alencibi27-arch/electronic-thermometer-kicad/AL-P060I.kicad_sch

## KiCad design AL-P060I.kicad_sch (2026-08-26)

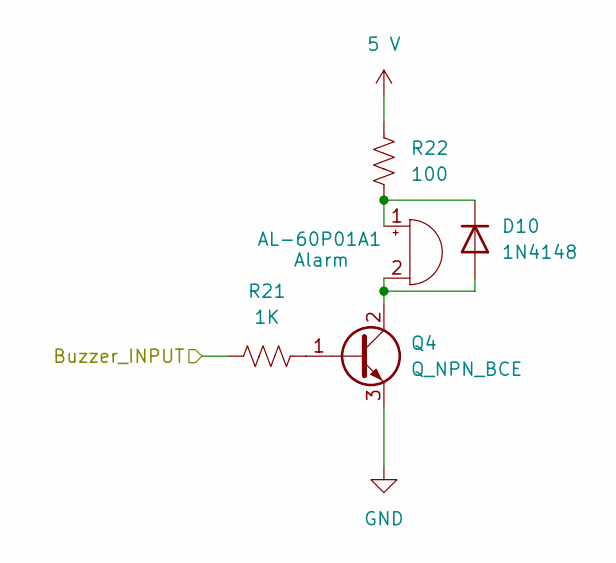
[picture p8: schematic AL-P060I.kicad_sch]

Parts:
AL-60P01A1: Alarm; AL-60P01A___; Rated Voltage 1.5V; Operating Voltage 1.5V
D10: 1N4148; D_SOD-123
Q4: Q_NPN_BCE; TO-92_Inline
R21: 1K; R_0805_2012Metric
R22: 100; R_0805_2012Metric

Connections:
Buzzer_INPUT: R21.1
GND: Q4.3 (E)
unnamed: AL-60P01A1.1 (+), D10.1 (K), R22.2
unnamed: AL-60P01A1.2 (-), D10.2 (A), Q4.2 (C)
unnamed: Q4.1 (B), R21.2
V: R22.1
