alencibi27-arch/electronic-thermometer-kicad/ALARM_SUBSYSTEM.kicad_sch

## KiCad design ALARM_SUBSYSTEM.kicad_sch (2026-08-26)

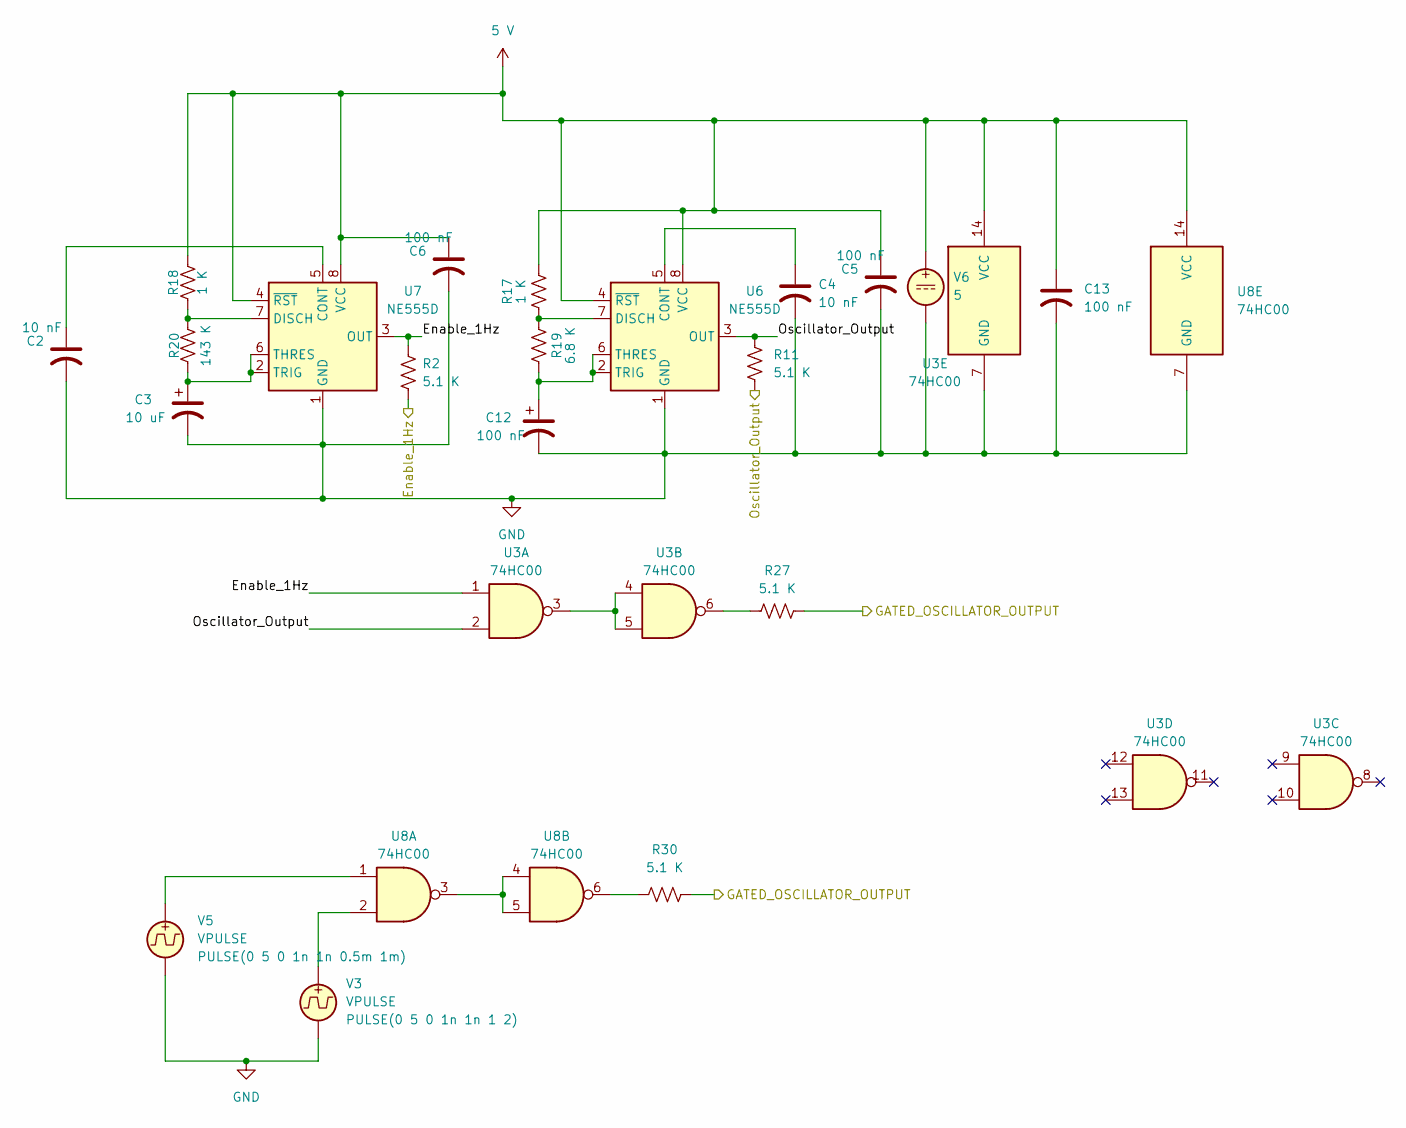
[picture p9: schematic ALARM_SUBSYSTEM.kicad_sch]

Parts:
C2, C4: 10 nF; C_1206_3216Metric
C3: 10 uF; CP_Radial_D5.0mm_P2.00mm
C5, C6, C13: 100 nF; C_1206_3216Metric
C12: 100 nF; CP_Radial_D5.0mm_P2.00mm
R2, R11, R27: 5.1 K; R_0805_2012Metric
R17, R18: 1 K; R_0805_2012Metric
R19: 6.8 K; R_0805_2012Metric
R20: 143 K; R_0805_2012Metric
R30: 5.1 K
U3: 74HC00; SOIC-14_3.9x8.7mm_P1.27mm
U6, U7: NE555D; SOIC-8_3.9x4.9mm_P1.27mm
U8: 74HC00
V3, V5: VPULSE
V6: 5

Connections:
Enable_1Hz: R2.1, R2.2, U3.1, U7.3 (OUT)
GATED_OSCILLATOR_OUTPUT: R27.1, R30.1
GND: C2.2, C3.2, C4.2, C5.2, C6.2, C12.2, C13.2, U3.7 (GND), U6.1 (GND), U7.1 (GND), U8.7 (GND), V3.2, V5.2, V6.2
unnamed: C2.1, U7.5 (CONT)
unnamed: C3.1, R20.1, U7.2 (TRIG), U7.6 (THRES)
unnamed: C4.1, U6.5 (CONT)
unnamed: C12.1, R19.2, U6.2 (TRIG), U6.6 (THRES)
unnamed: R17.1, R19.1, U6.7 (DISCH)
unnamed: R18.1, R20.2, U7.7 (DISCH)
unnamed: R27.2, U3.6
unnamed: R30.2, U8.6
unnamed: U3.3, U3.4, U3.5
unnamed: U8.1, V5.1
unnamed: U8.2, V3.1
unnamed: U8.3, U8.4, U8.5
Oscillator_Output: R11.1, R11.2, U3.2, U6.3 (OUT)
V: C5.1, C6.1, C13.1, R17.2, R18.2, U3.14 (VCC), U6.4 (~RST), U6.8 (VCC), U7.4 (~RST), U7.8 (VCC), U8.14 (VCC), V6.1
