alencibi27-arch/electronic-thermometer-kicad/LED_STEP_DECODER.kicad_sch

## KiCad design LED_STEP_DECODER.kicad_sch (2026-08-26)

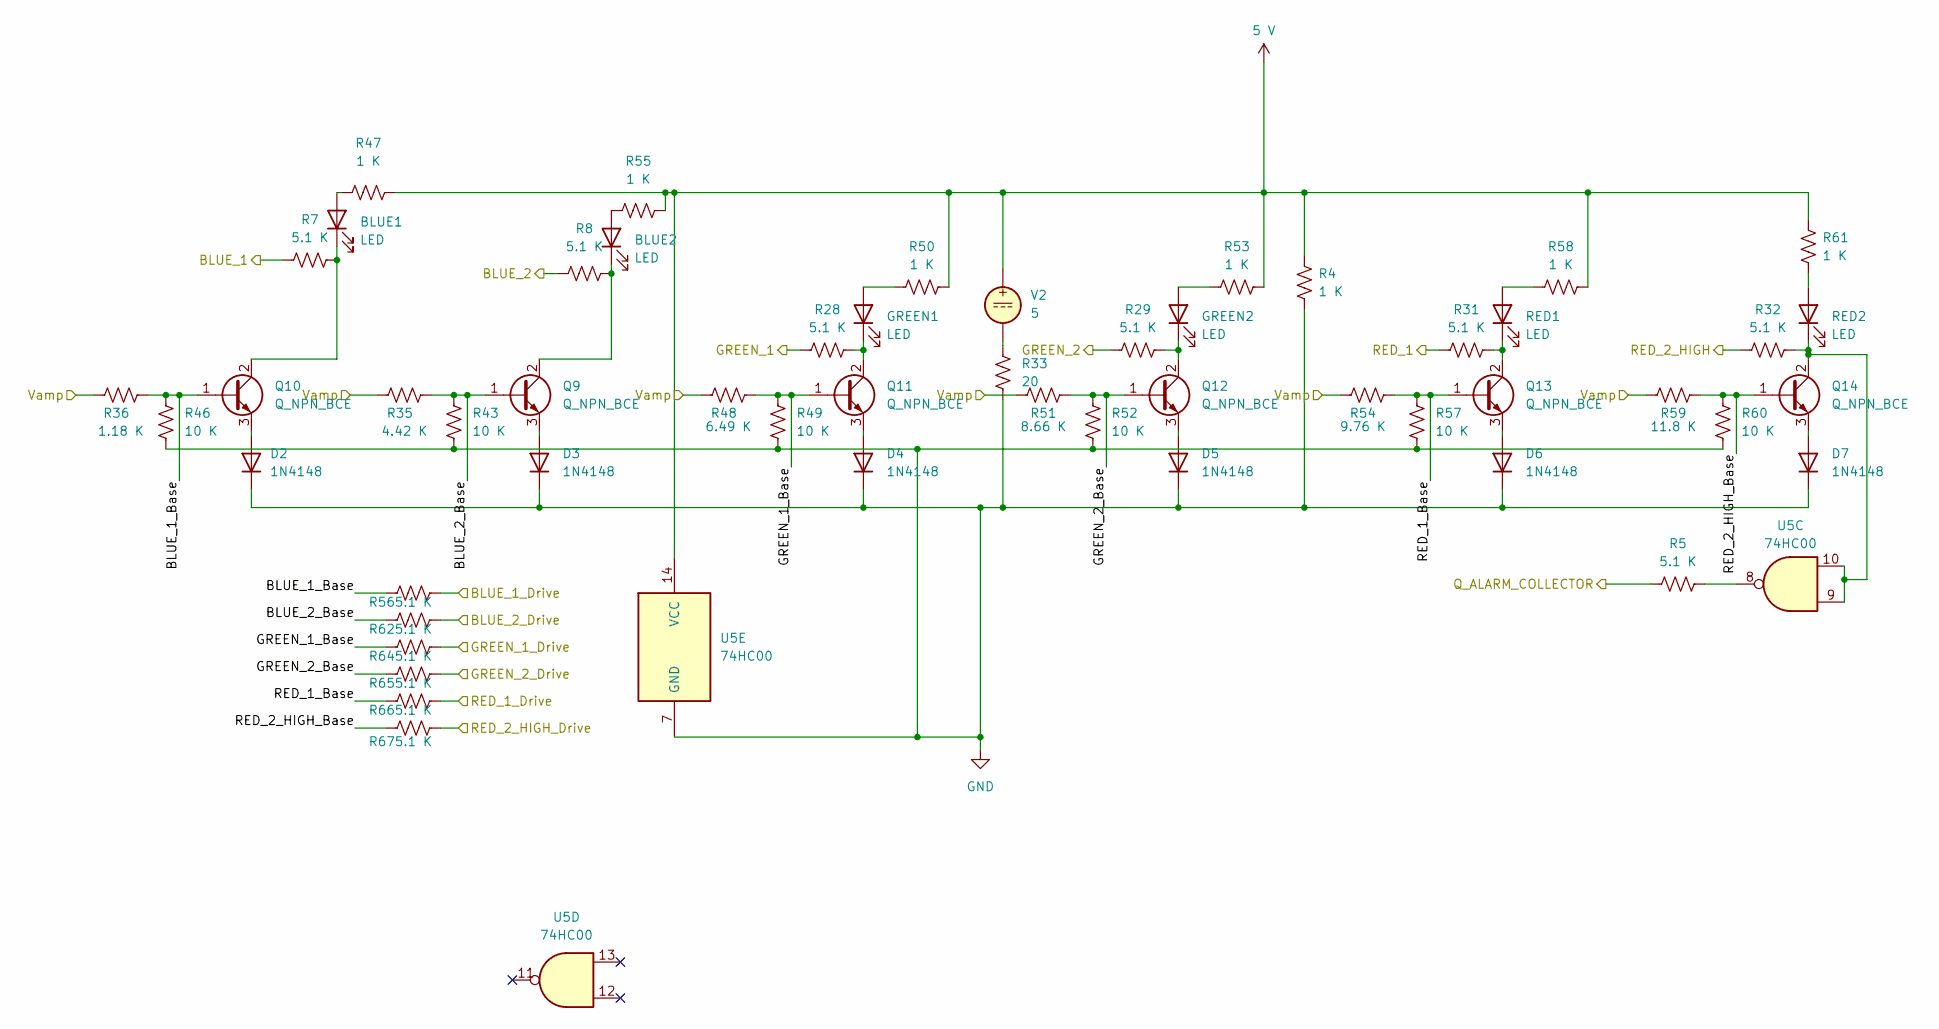
[picture p10: schematic LED_STEP_DECODER.kicad_sch]

Parts:
BLUE1, BLUE2: LED; LED_0805_2012Metric
D2, D3, D4, D5, D6, D7: 1N4148; D_DO-35_SOD27_P7.62mm_Horizontal
GREEN1, GREEN2: LED; LED_0805_2012Metric
Q9, Q10, Q11, Q12, Q13, Q14: Q_NPN_BCE; TO-92_Inline
R4, R47, R50, R53, R55, R58, R61: 1 K; R_0805_2012Metric
R5, R7, R8, R28, R29, R31, R32, R56, R62, R64, R65, R66, R67: 5.1 K; R_0805_2012Metric
R33: 20; R_0805_2012Metric
R35: 4.42 K; R_0805_2012Metric
R36: 1.18 K; R_0805_2012Metric
R43, R46, R49, R52, R57, R60: 10 K; R_0805_2012Metric
R48: 6.49 K; R_0805_2012Metric
R51: 8.66 K; R_0805_2012Metric
R54: 9.76 K; R_0805_2012Metric
R59: 11.8 K; R_0805_2012Metric
RED1, RED2: LED; LED_0805_2012Metric
U5: 74HC00; SOIC-14_3.9x8.7mm_P1.27mm
V2: 5

Connections:
BLUE_1: R7.1
BLUE_1_Base: Q10.1 (B), R36.2, R46.1, R56.1
BLUE_1_Drive: R56.2
BLUE_2: R8.1
BLUE_2_Base: Q9.1 (B), R35.2, R43.1, R62.1
BLUE_2_Drive: R62.2
GND: D2.1 (K), D3.1 (K), D4.1 (K), D5.1 (K), D6.1 (K), D7.1 (K), R4.2, R33.1, R43.2, R46.2, R49.2, R52.2, R57.2, R60.2, U5.7 (GND)
GREEN_1: R28.1
GREEN_1_Base: Q11.1 (B), R48.2, R49.1, R64.1
GREEN_1_Drive: R64.2
GREEN_2: R29.1
GREEN_2_Base: Q12.1 (B), R51.2, R52.1, R65.1
GREEN_2_Drive: R65.2
unnamed: BLUE1.1 (K), Q10.2 (C), R7.2
unnamed: BLUE1.2 (A), R47.1
unnamed: BLUE2.1 (K), Q9.2 (C), R8.2
unnamed: BLUE2.2 (A), R55.1
unnamed: D2.2 (A), Q10.3 (E)
unnamed: D3.2 (A), Q9.3 (E)
unnamed: D4.2 (A), Q11.3 (E)
unnamed: D5.2 (A), Q12.3 (E)
unnamed: D6.2 (A), Q13.3 (E)
unnamed: D7.2 (A), Q14.3 (E)
unnamed: GREEN1.1 (K), Q11.2 (C), R28.2
unnamed: GREEN1.2 (A), R50.1
unnamed: GREEN2.1 (K), Q12.2 (C), R29.2
unnamed: GREEN2.2 (A), R53.1
unnamed: Q13.2 (C), R31.2, RED1.1 (K)
unnamed: Q14.2 (C), R32.2, RED2.1 (K), U5.9, U5.10
unnamed: R5.2, U5.8
unnamed: R33.2, V2.2
unnamed: R58.1, RED1.2 (A)
unnamed: R61.1, RED2.2 (A)
Q_ALARM_COLLECTOR: R5.1
RED_1: R31.1
RED_1_Base: Q13.1 (B), R54.2, R57.1, R66.1
RED_1_Drive: R66.2
RED_2_HIGH: R32.1
RED_2_HIGH_Base: Q14.1 (B), R59.2, R60.1, R67.1
RED_2_HIGH_Drive: R67.2
V: R4.1, R47.2, R50.2, R53.2, R55.2, R58.2, R61.2, U5.14 (VCC), V2.1
Vamp: R35.1, R36.1, R48.1, R51.1, R54.1, R59.1
