alencibi27-arch/electronic-thermometer-kicad/LM235_Temp_Sensor.kicad_sch

## KiCad design LM235_Temp_Sensor.kicad_sch (2026-08-26)

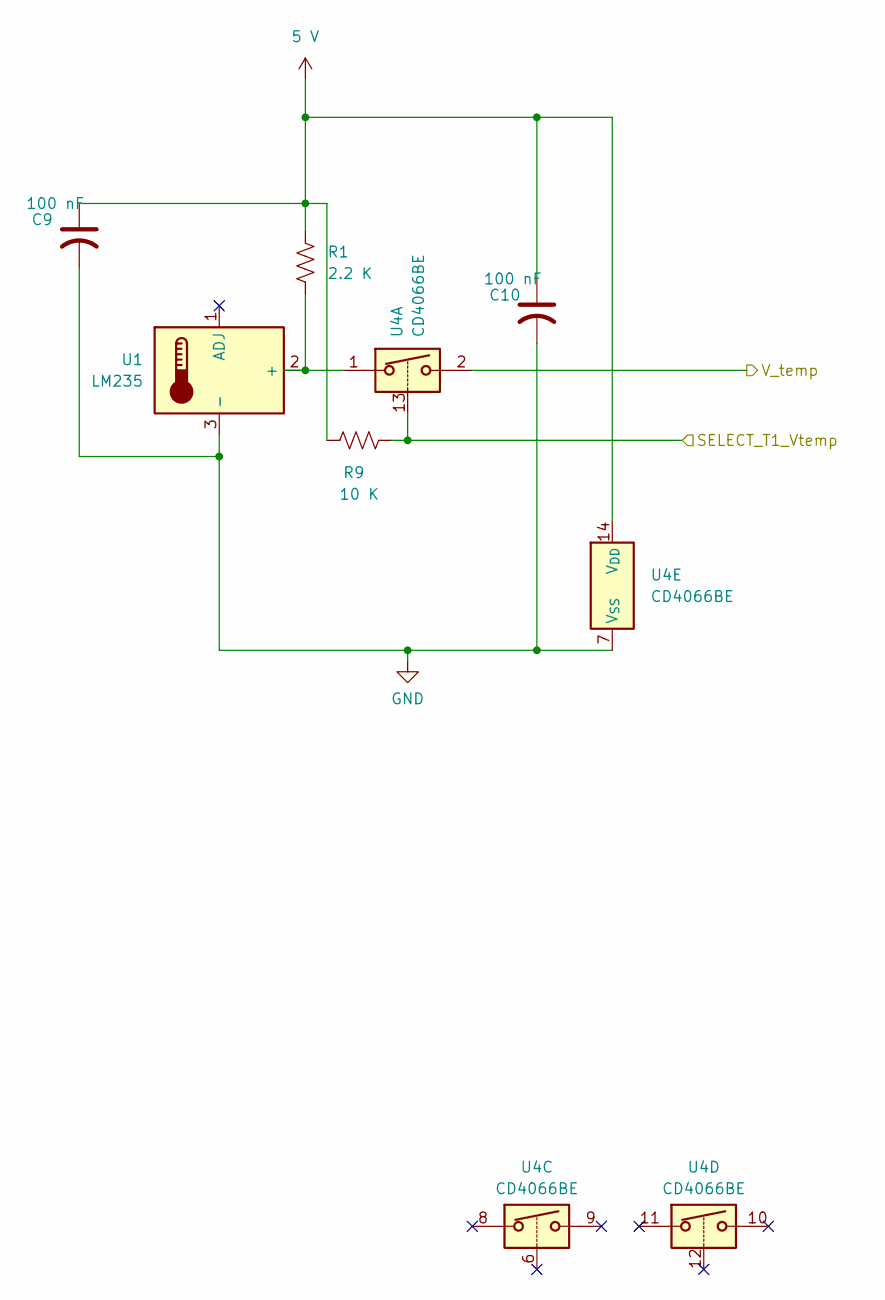
[picture p11: schematic LM235_Temp_Sensor.kicad_sch]

Parts:
C9, C10: 100 nF; C_1206_3216Metric
R1: 2.2 K; R_0805_2012Metric
R9: 10 K; R_0805_2012Metric
U1: LM235; TO-92L_Inline_Wide
U4: CD4066BE; DIP-14_W7.62mm

Connections:
GND: C9.2, C10.2, U1.3 (-), U4.7 (V_{SS})
unnamed: R1.2, U1.2 (+), U4.1
SELECT_T1_Vtemp: R9.2, U4.13
V: C9.1, C10.1, R1.1, R9.1, U4.14 (V_{DD})
V_temp: U4.2
