alencibi27-arch/electronic-thermometer-kicad/OP_AMPLIFIER.kicad_sch

## KiCad design OP_AMPLIFIER.kicad_sch (2026-08-26)

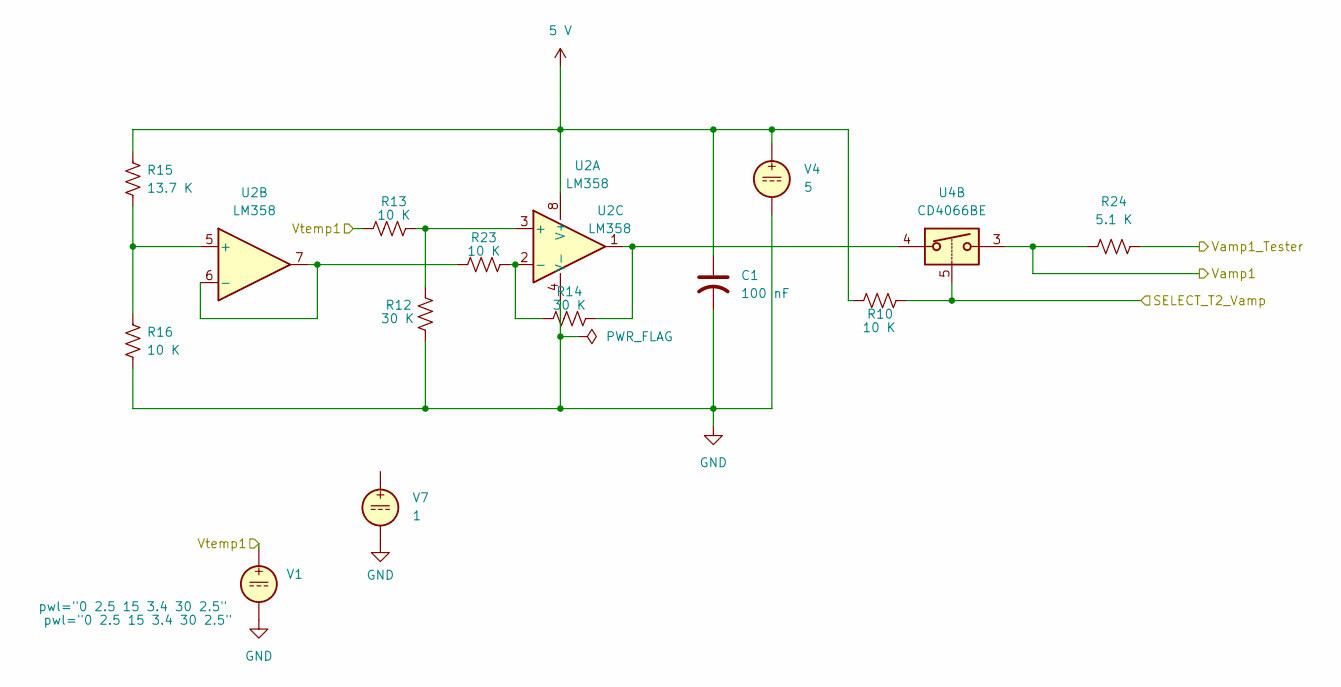
[picture p12: schematic OP_AMPLIFIER.kicad_sch]

Parts:
C1: 100 nF; C_1206_3216Metric
R10, R13, R16, R23: 10 K; R_0805_2012Metric
R12, R14: 30 K; R_0805_2012Metric
R15: 13.7 K; R_0805_2012Metric
R24: 5.1 K; R_0805_2012Metric
U2: LM358; SOIC-8_3.9x4.9mm_P1.27mm
U4: CD4066BE; DIP-14_W7.62mm
V1: pwl="0 2.5 15 3.4 30 2.5"
V4: 5
V7: 1

Connections:
GND: C1.2, R12.2, R16.2, U2.4 (V-), V1.2, V4.2, V7.2
unnamed: R12.1, R13.2, U2.3 (+)
unnamed: R14.1, R23.2, U2.2 (-)
unnamed: R14.2, U2.1, U4.4
unnamed: R15.2, R16.1, U2.5 (+)
unnamed: R23.1, U2.6 (-), U2.7
SELECT_T2_Vamp: R10.1, U4.5
V: C1.1, R10.2, R15.1, U2.8 (V+), V4.1
Vamp1: R24.1, U4.3
Vamp1_Tester: R24.2
Vtemp1: R13.1, V1.1
